kasitoru/esp_radiation_meter/photos/IMG_0110.JPG

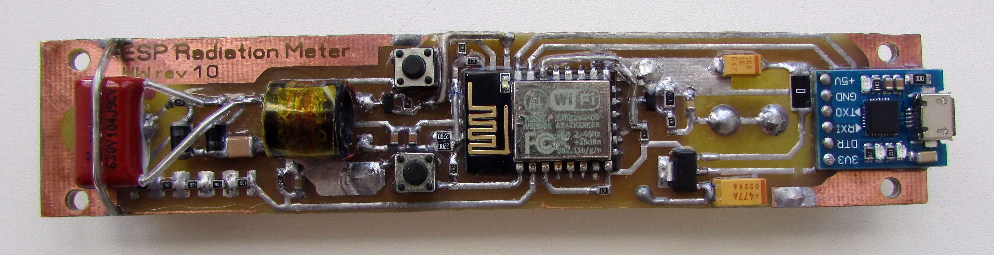
photos/IMG_0110.JPG
