kasitoru/esp_radiation_meter/photos/IMG_0111.JPG

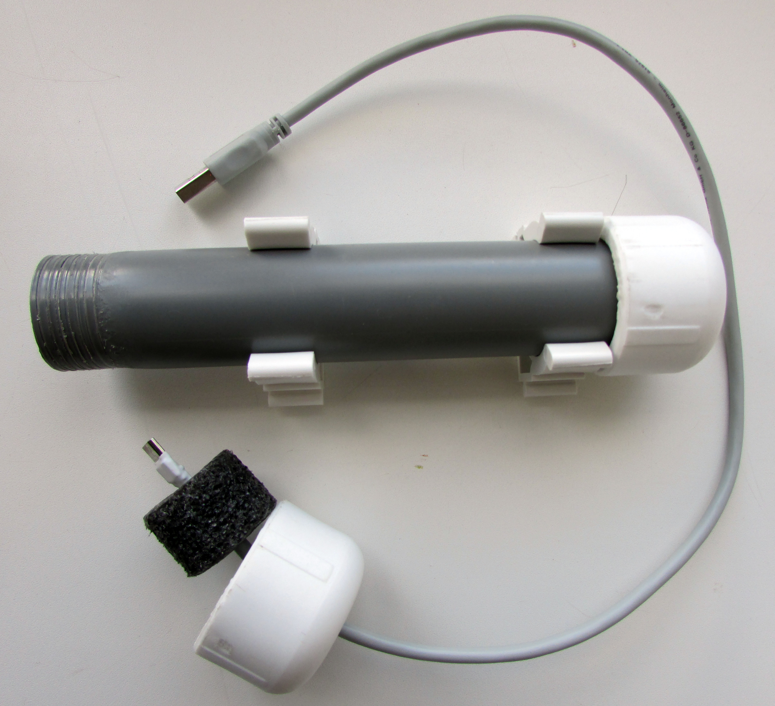
photos/IMG_0111.JPG
